UnusedSpace/MarlinFw/marlinfw/datasheets/skr_1.4_turbo/skr_1.4_turbo_stedir-diagram.jpg

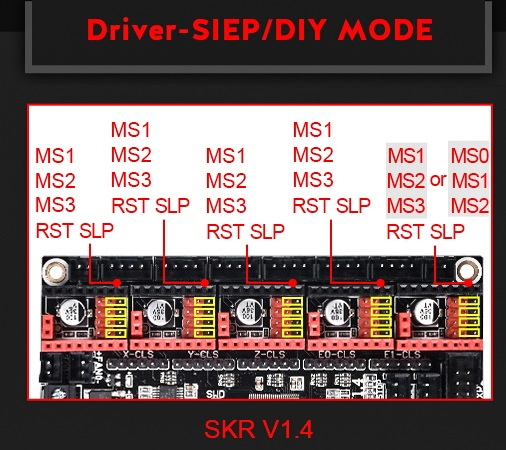
marlinfw/datasheets/skr_1.4_turbo/skr_1.4_turbo_stedir-diagram.jpg
