UnusedSpace/MarlinFw/marlinfw/datasheets/skr_1.4_turbo/skr_1.4_turbo_uart.jpg

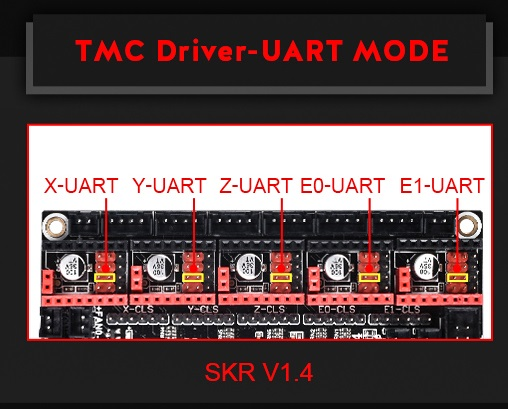
marlinfw/datasheets/skr_1.4_turbo/skr_1.4_turbo_uart.jpg
